marierm/quintet/pcb/export/sponge2_PCB1_57470_etch_silk_bottom.pdf

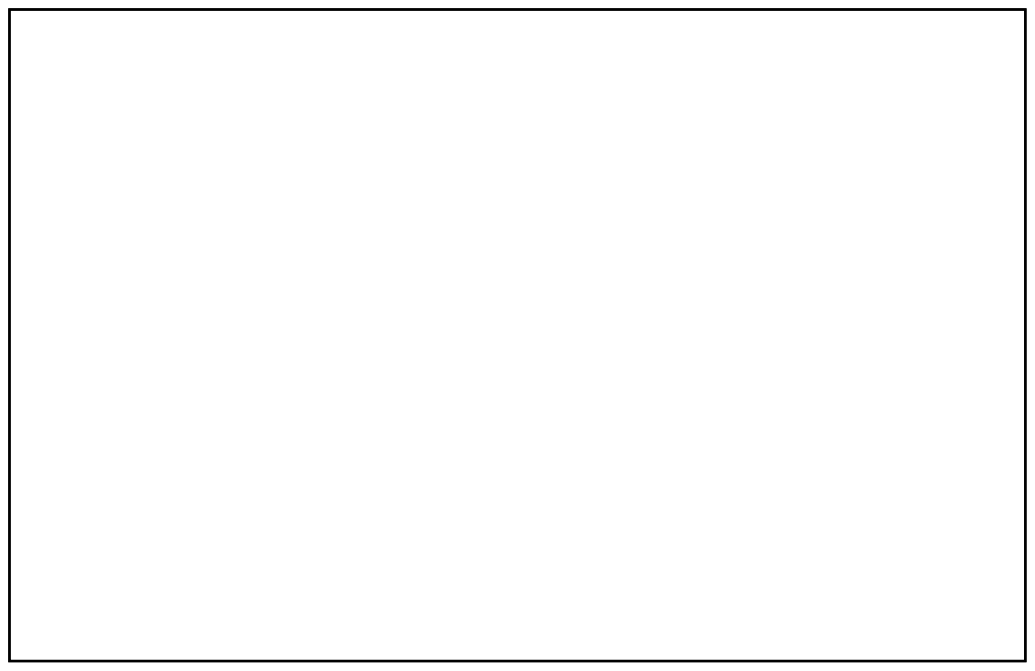
[picture p9: page 1]
