marierm/quintet/pcb/export/sponge2_PCB1_57470_etch_silk_bottom_mirror.pdf

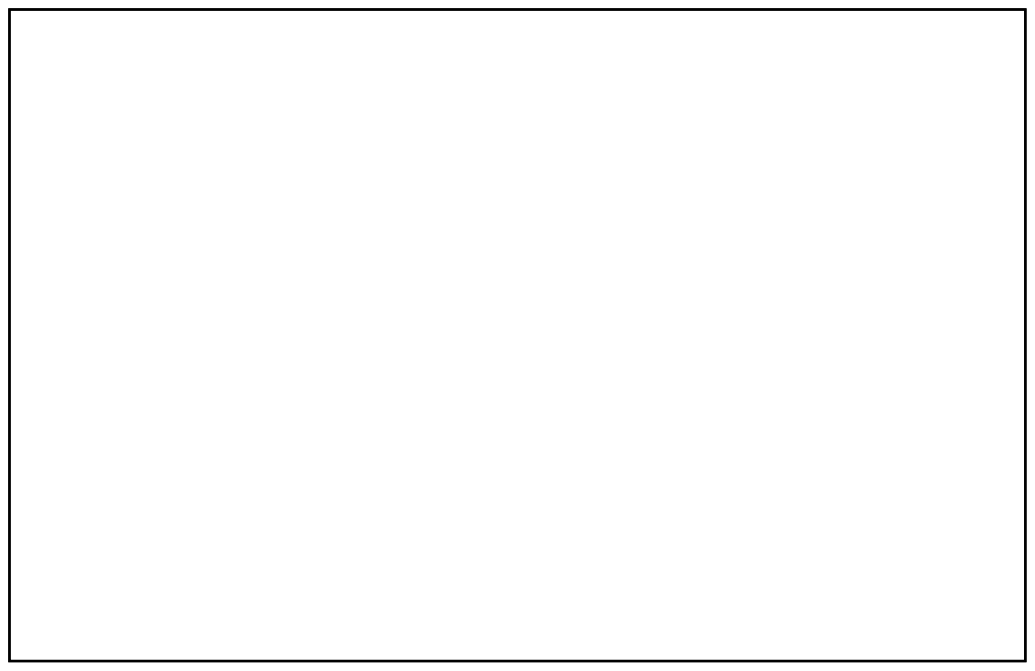
[picture p10: page 1]
