marierm/quintet/pcb/export/sponge2_PCB1_57470_etch_silk_top.pdf

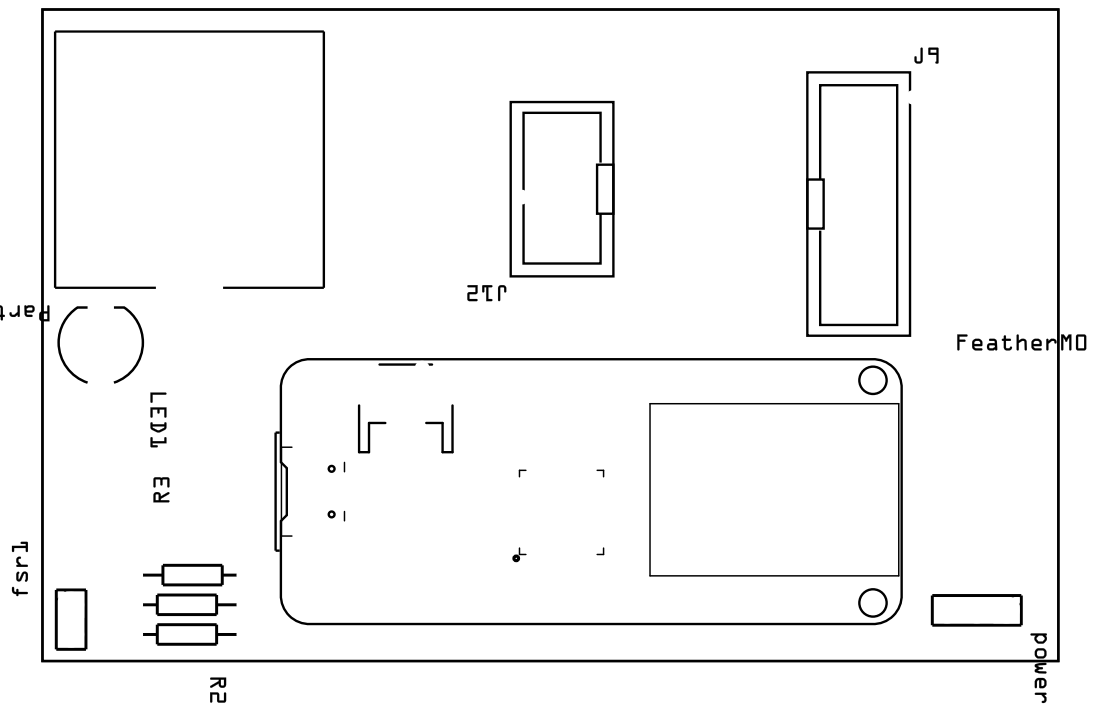
[picture p11: page 1]
