marierm/quintet/pcb/export/sponge2_PCB1_57470_etch_silk_top_mirror.pdf

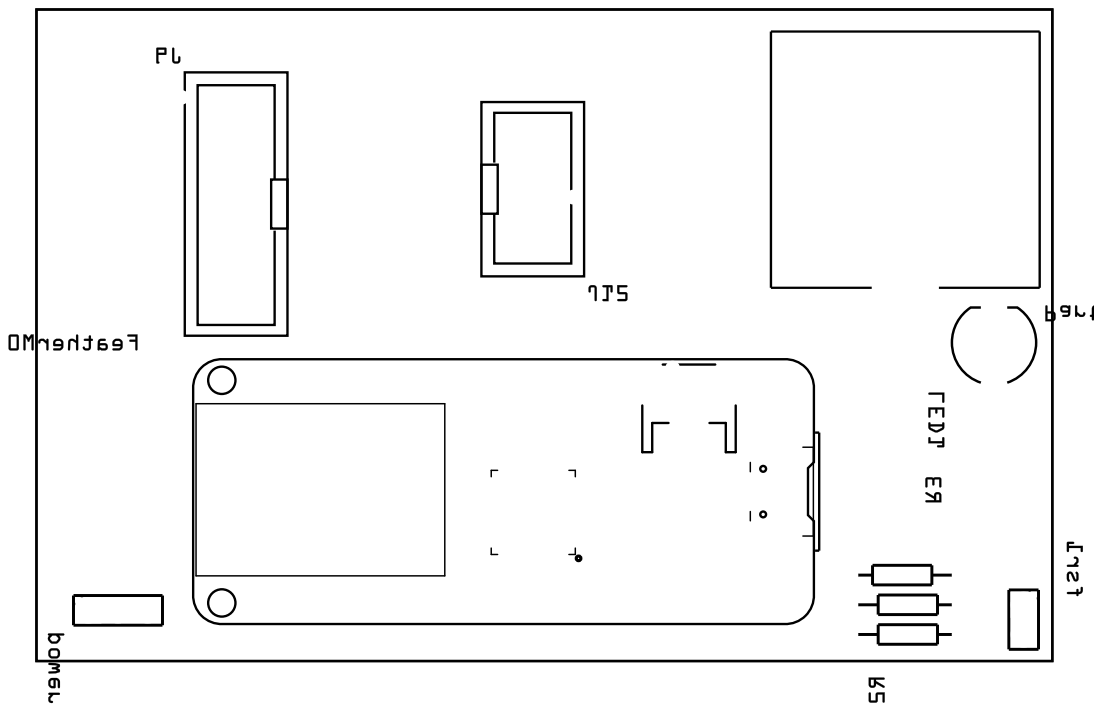
[picture p12: page 1]
